felixwittwer/the_multikeyboard/images/without_keys_and_switches.png

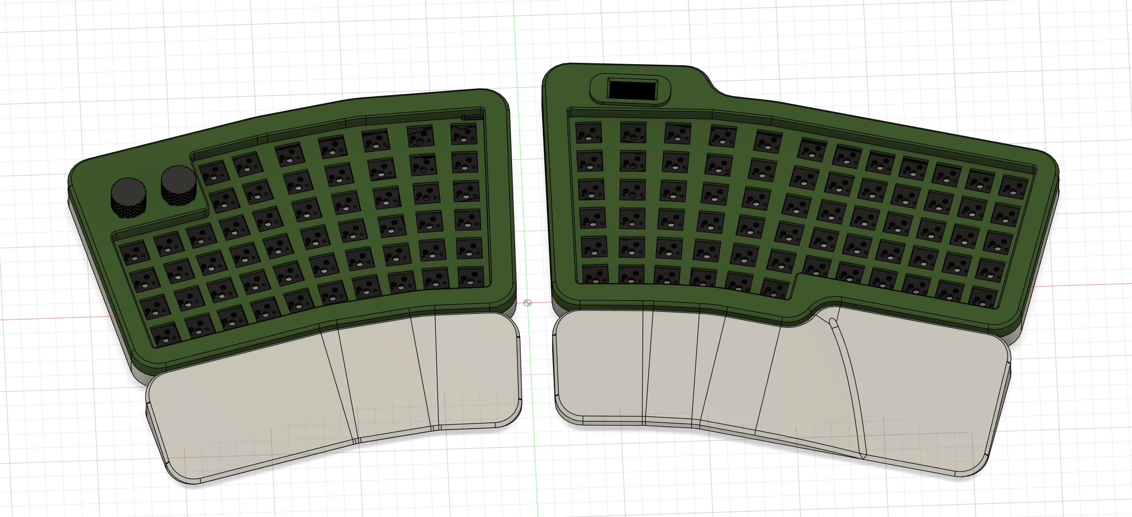
images/without_keys_and_switches.png
