felixwittwer/the_multikeyboard/pcb/LEFT_Main/multiboard_LEFT.png

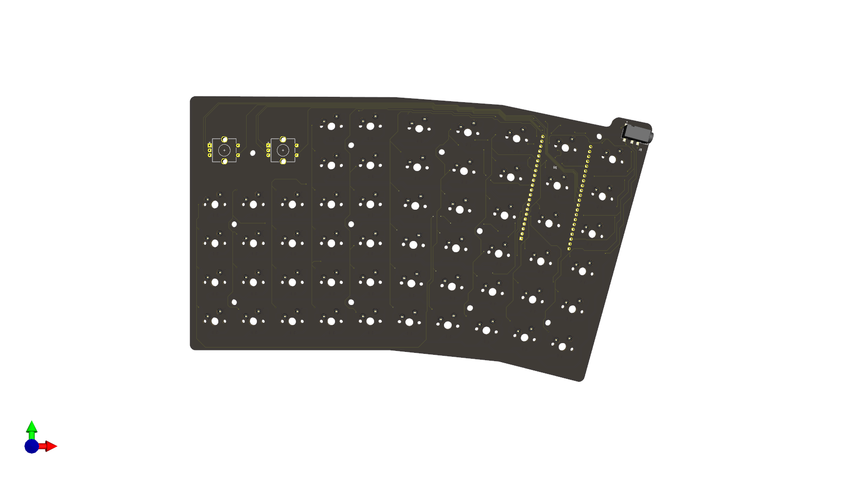
pcb/LEFT_Main/multiboard_LEFT.png
