felixwittwer/the_multikeyboard/pcb/RIGHT_Main/multiboard_RIGHT.png

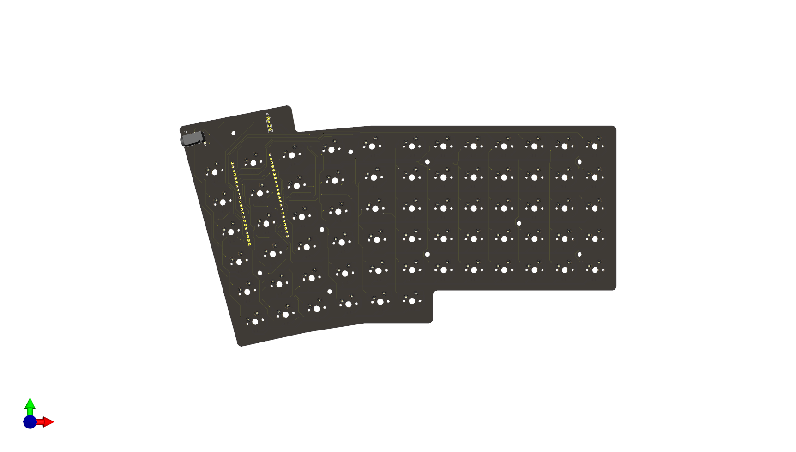
pcb/RIGHT_Main/multiboard_RIGHT.png
